trailcurrentoss/TrailCurrentReservoir/DOCS/img/MakerworldPhotos/ModelPic_02_ConnectorSide_CoverOff.jpg

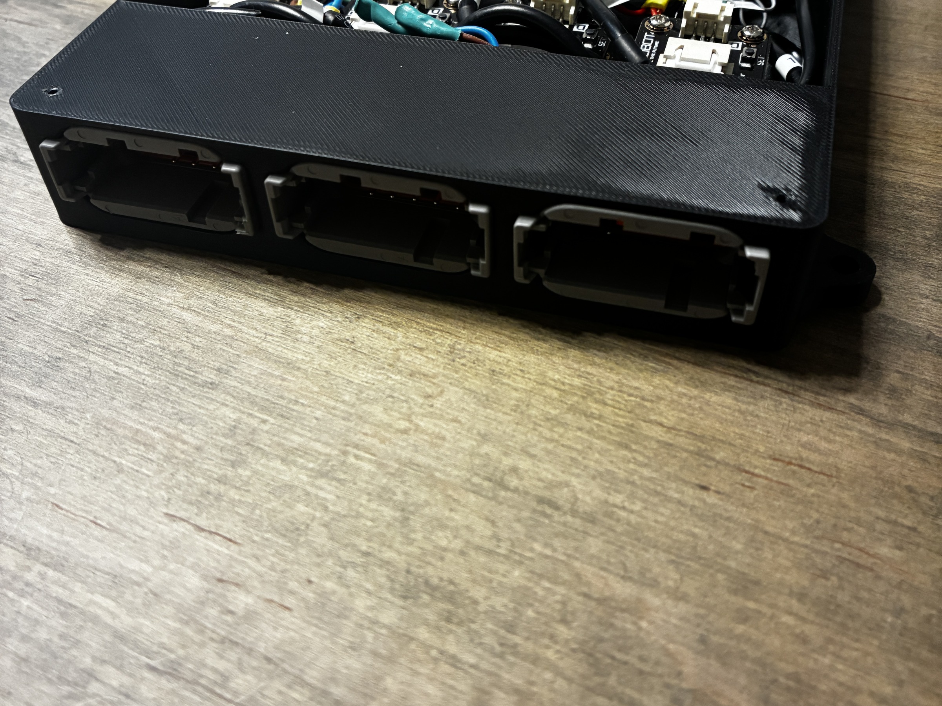
DOCS/img/MakerworldPhotos/ModelPic_02_ConnectorSide_CoverOff.jpg
