trailcurrentoss/TrailCurrentReservoir/DOCS/img/MakerworldPhotos/ModelPic_05_Assembled_Angle1.jpg

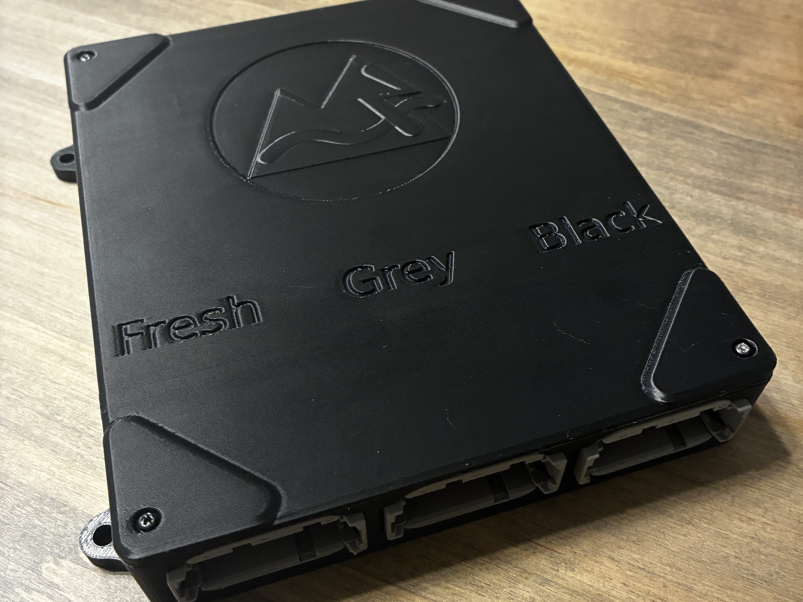
DOCS/img/MakerworldPhotos/ModelPic_05_Assembled_Angle1.jpg
